todbot/pico_test_synth/circuitpython/tbish/tbish_sequencer.py

# SPDX-FileCopyrightText: Copyright (c) 2025 Tod Kurt
# SPDX-License-Identifier: MIT

import time

class TBishSequencer:
    def __init__(self, tb, steps_per_beat=4, bpm=120, seqs=None):
        self.tb = tb
        self.seqs = seqs
        self._steps_per_beat = steps_per_beat   # 4 = 16th note, 2 = 8th note, 1 = quarter note
        self.bpm = bpm
        self.gate_time = 0
        self.gate_amount = 0.75  # traiditional 303 gate length
        self.next_step_time = 0
        self.gate_off_time = 0
        self.midi_note = 0   # current note being played or 0 for none
        self.seqs = seqs
        self.seq_num = 0
        self.transpose = 0
        self.i = 0  # step number
        self.playing = True
        self.on_step_callback = None   # callback is func(step, steps_per_beat, seq_len)

    @property
    def steps_per_beat(self):
        return self._steps_per_beat
    
    @steps_per_beat.setter
    def steps_per_beat(self, s):
        self._steps_per_beat = s
        self._secs_per_step = 60 / self._bpm / self._steps_per_beat       
    
    @property
    def bpm(self):
        return self._bpm
    
    @bpm.setter
    def bpm(self, b):
        self._bpm = b
        self._secs_per_step = 60 / self._bpm / self._steps_per_beat

    def start(self):
        self.playing = True
        self.i = 0
        self.next_step_time = time.monotonic()

    def stop(self):
        self.playing = False
        self.tb.note_off(self.midi_note)

    def update(self):
        
        now = time.monotonic()
    
        # turn off note (not really a TB-303 thing, but a MIDI thing)
        if self.gate_off_time and self.gate_off_time - now <= 0:
            self.gate_off_time = 0
            self.tb.note_off(self.midi_note)

        # time for next step? 
        dt = (self.next_step_time - now)
        if dt <= 0:
            self.next_step_time = now + self._secs_per_step + dt  
            # add dt delta to attempt to make up for display hosing us
            
            seq_len = len(self.seqs[self.seq_num][0])
            if self.on_step_callback:  # and (self.i % self._steps_per_beat)==0:
                self.on_step_callback(self.i, self.steps_per_beat, seq_len)

            if not self.playing:
                return
            
            midi_note = self.seqs[self.seq_num][0][self.i]
            vel       = self.seqs[self.seq_num][1][self.i]
            if midi_note != 0:    # midi_note == 0 = rest
                midi_note += self.transpose
                vel = vel  # + random.randint(-30,0)
                self.tb.secs_per_step = self._secs_per_step * 1.0
                self.tb.note_on(midi_note, vel)
                #self.tb.note_on(midi_note, True, False)
                self.gate_off_time = time.monotonic() + self._secs_per_step * self.gate_amount

            #seq_num = int(param_set.param_for_name('seq').val)
            self.i = (self.i+1) % seq_len
            self.midi_note = midi_note
        
            print("step", self.i,"note: %d vel:%3d" % (midi_note, vel),
                  int(self._secs_per_step*1000), int(dt*1000))
