todbot/pico_test_synth/arduino/monosynth1/SynthUI.h

#ifndef SYNTHUI_H
#define SYNTHUI_H

#include <stdio.h>
#include <stdarg.h>
#include <Adafruit_GFX.h>

#define KEY_NONE 0    // No key presses are detected
#define KEY_UP 1      // Up key is pressed (navigate up through the menu items list, select next value of the digit/char of editable variable, or previous option in select)
#define KEY_RIGHT 2   // Right key is pressed (navigate through the link to another (child) menu page, select next digit/char of editable variable, execute code associated with button)
#define KEY_DOWN 3    // Down key is pressed (navigate down through the menu items list, select previous value of the digit/char of editable variable, or next option in select)
#define KEY_LEFT 4    // Left key is pressed (navigate through the Back button to the previous menu page, select previous digit/char of editable variable)
#define KEY_CANCEL 5  // Cancel key is pressed (navigate to the previous (parent) menu page, exit edit mode without saving the variable, exit context loop if allowed within context's settings)
#define KEY_OK 6      // Ok/Apply key is pressed (toggle bool menu item, enter edit mode of the associated non-bool variable, exit edit mode with saving the variable, execute code associated with button)


class SynthUI {
public:
  SynthUI(Adafruit_GFX* adisplay) {
    display = adisplay;
  }

  void set_font(const GFXfont* fnt = NULL) {
    display->setFont(fnt);
  }
  
  /** 
   * Print text at a given x,y, using an optionally specified font
   */
  void print_text(int x, int y, const char* str, const GFXfont* fnt = NULL) {
    if (fnt != NULL) { display->setFont(fnt); }
    display->setTextColor(WHITE, 0);
    display->setCursor(x, y);
    display->print(str);
  }

  void print_textf(int x, int y, const char* fmt, ...) {
    char buf[80];
    va_list va;
    va_start(va, fmt);
    vsnprintf(buf, 80, fmt, va);
    va_end(va);
    print_text(x, y, buf);
  }

  /** 
   * Draw vertical slider with a "thumb" position identifying value
   * thumpos ranges 0.0-1.0
   */
  void draw_vertical_slider(int x, int y, float thumbpos, int w = 5, int h = 63, int thumbw = 0, int thumbh = 10) {
    int ypos = thumbpos * h;
    thumbw = (thumbw == 0) ? w : thumbw;  // make thumbw same width as slider if not specified
    display->drawRect(x, y, w, h, WHITE);
    display->fillRect(x, y + ypos, thumbw, thumbh, WHITE);
  }
  /** 
   * Draw horizontal slider with a "thumb" position identifying value
   * thumpos ranges 0.0-1.0
   */
  void draw_horizontal_slider(int x, int y, float thumbpos, int w = 127, int h = 5, int thumbw = 10, int thumbh = 0) {
    int xpos = thumbpos * (w - thumbw);
    thumbh = (thumbh == 0) ? h : thumbh;  // make thumbh same height as slider if not specified
    display->drawRect(x, y - h, w, h, WHITE);
    display->fillRect(x + xpos, y - h, thumbw, thumbh, WHITE);
  }


  Adafruit_GFX* display;
};

#endif
